leojpod/harmonica-case/pictures/IMG_20221201_210023.jpg

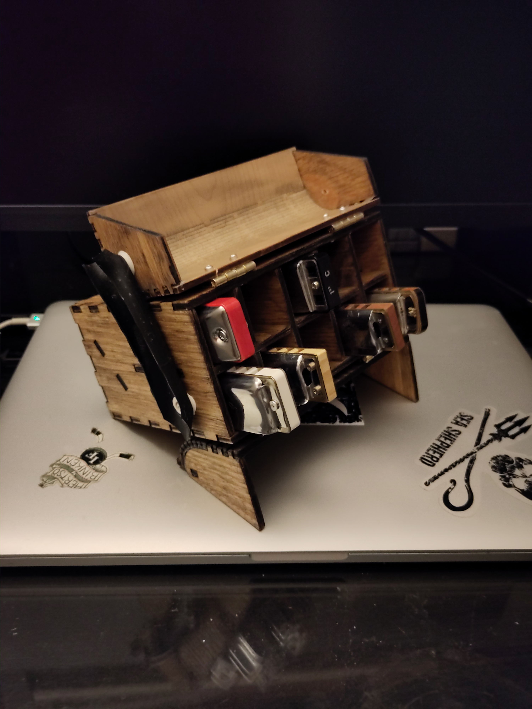
pictures/IMG_20221201_210023.jpg
