leojpod/harmonica-case/3d-models/utils/cylinder-outer.scad

module cylinder_outer(height,radius,fn){
  fudge = 1/cos(180/fn);
  cylinder(h=height,r=radius*fudge,$fn=fn);
}
