leojpod/harmonica-case/pictures/IMG_20221201_205339.jpg

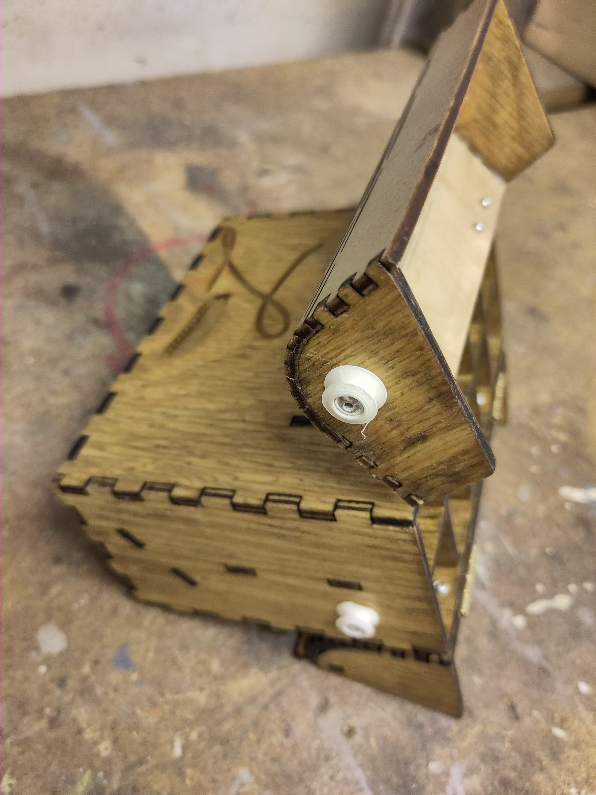
pictures/IMG_20221201_205339.jpg
